dcooperdalrymple/C64UserPortMidi/monitor/routines.asm

;=======================================
; Print
; -----
; X - Lo byte of string memory location
; Y - Hi byte of string memory location
;
; String data must end with EOF.
; Max length of 40?
;=======================================

Print:
    stx temp+0
    sty temp+1

    ldy #0
Print_chr:
    lda (temp),y
    cmp #EOF
    beq Print_done
    jsr CHROUT

    iny
    jmp Print_chr

Print_done:
    rts

;============================================
; PrintHex
; -----
; A - Byte value to be printed as hex string
;============================================

PrintHex:
    tax

    ; Top nibble
    and #%11110000
    REPEAT 4
    lsr
    REPEND
    tay
    lda hex_data,y
    sta hexstr+1

    ; Bottom nibble
    txa
    and #%00001111
    tay
    lda hex_data,y
    sta hexstr+2

    ; Hex indicator icon "$"
    lda hex_prepend
    sta hexstr+0

    ; Check if new line or space
    lda #SPACE
    inc linelen
    ldx linelen
    cpx #HEX_LINE_MAX
    bne PrintHex_append

    ; Reset line length
    lda #0
    sta linelen

    lda #EOL
PrintHex_append:
    sta hexstr+3

    ; String end indicator
    lda #EOF
    sta hexstr+4

    ldx #<hexstr
    ldy #>hexstr
    jsr Print

    rts

;================================================
; PrintDec
; -----
; A - Byte value to be printed as decimal string
;================================================

PrintDec:
    sta temp+0

    ; Switch to decimal mode
    clc
    sed

    ; Clear result
    lda #0
    sta temp+1
    sta temp+2

    ldx #8 ; bits
PrintDec_bit:
    asl temp+0 ; shift out bit

    ; add into result
    lda temp+1
    adc temp+1
    sta temp+1

    ; propagate any carry
    lda temp+2
    adc temp+2
    sta temp+2

    ; repeat for next bit
    dex
    bne PrintDec_bit

    ; Back to binary
    cld

    ldy #2
    sty temp+3
PrintDec_loop:

    ; Top nibble
    lda temp,y
    and #$f0
    REPEAT 4
    lsr
    REPEND
    adc #$30
    jsr CHROUT

    ; Bottom nibble
    ldy temp+3
    lda temp,y
    and #$0f
    adc #$30
    jsr CHROUT

    dec temp+3
    ldy temp+3
    bne PrintDec_loop

    ; Space or line at the end
    lda #SPACE
    inc linelen
    ldx linelen
    cpx #DEC_LINE_MAX
    bne PrintDec_append

    ; Reset linelen
    lda #0
    sta linelen

    lda #EOL
PrintDec_append:
    jsr CHROUT

    rts

;=================================================
; PrintNibble
; -----
; A - Byte value to be printed as decimal string,
;     but just the first 4 bits
;=================================================

PrintNibble:
    REPEAT 4
    asl
    REPEND
    sta temp+0

    ; Switch to decimal mode
    clc
    sed

    ; Clear result
    lda #0
    sta temp+1

    ldx #4 ; bits
PrintNibble_bit:
    asl temp+0 ; shift out bit

    ; add into result
    lda temp+1
    adc temp+1
    sta temp+1

    ; repeat for next bit
    dex
    bne PrintNibble_bit

    ; Back to binary
    cld

    ; Top nibble
    lda temp+1
    and #$f0
    REPEAT 4
    lsr
    REPEND
    adc #$30
    jsr CHROUT

    ; Bottom nibble
    lda temp+1
    and #$0f
    adc #$30
    jsr CHROUT

    ; Space at the end
    jsr PrintSpace

    rts

;===========
; PrintLine
;===========

PrintLine:
    lda #EOL
    jsr CHROUT

    lda #0
    sta linelen

    rts

;============
; PrintSpace
;============

PrintSpace:
    lda #SPACE
    jsr CHROUT

    rts

;=================================
; PrintMidi
; ---------
; Prints out full midi message
; based on variables (mcomm, etc)
;=================================

PrintMidi:

    ; Print MIDI command name
    lda mcomm
    asl
    tay
    ldx midi_comm_strs,y
    iny
    lda midi_comm_strs,y
    tay
    jsr Print

    jsr PrintSpace

    ; Print channel nibble
    ldx #<midi_chan_str
    ldy #>midi_chan_str
    jsr Print

    lda mchan
    jsr PrintNibble

    ; Print data
    ldx #<midi_data_str
    ldy #>midi_data_str
    jsr Print

    ldy #0
    sty temp+3
PrintMidi_data:
    lda mdata,y
    jsr PrintHex

    inc temp+3
    ldy temp+3
    cpy mlen
    bne PrintMidi_data

    ; Finish up with a line return
    jsr PrintLine

    rts
